joachimth/mk3-reference-loudspeaker/assets/datasheets/15W-4434G00.md

# ScanSpeak 15W/4434G00 — Datasheet Reference

**Source:** [Official ScanSpeak product page](https://www.scan-speak.dk/product/15w-4434g00/) + [official datasheet PDF (319KB)](./15W-4434G00.pdf) + ScanSpeak mounting drawing (embedded in PDF, extracted visually).

**Driver family:** Discovery series, 15 cm midwoofer, 4 Ω.
**Role in mk2:** Midrange driver.

---

## Mechanical dimensions (from official mounting drawing)

| Parameter | Value | Tolerance | Symbol / use in SCAD |
|---|---|---|---|
| Faceplate outer diameter | **149.3 mm** | ±0.5 | `mid_face_d` |
| Mounting BCD ("Pitch diam", 4-hole pattern) | **136.5 mm** | — | `mid_bcd` |
| Mounting hole diameter | **5.3 mm** | ±0.1 (×4 holes, 90° apart) | `mid_hole_d` |
| Number of mounting holes | **4** | — | `mid_holes` |
| Total depth (incl. front flange) | **61.9 mm** | — | `mid_depth` |
| Front flange thickness | **4.8 mm** | — | `mid_flange_t` (flush-mount rebate depth) |
| Basket / magnet system OD behind flange | **114 mm** (+2/0), Ø90 inner | — | `mid_basket_d` |
| Effective diaphragm diameter | 101 mm | — | (T-S only, not a mounting dim) |
| Cabinet displacement volume | **0.23 L** | — | `mid_displ_L` (datasheet "Mechanical Data") |
| Baffle cutout diameter | **not specified on drawing** — ~Ø123 estimate | — | `mid_cut_d` (must clear the Ø114 basket AND leave screw land inside the Ø136.5 BCD; caliper-verify) |

> **Source-of-truth:** values re-extracted July 2026 directly from the dimension
> drawing in `15W-4434G00.pdf`. An earlier version of this table (104.0 / 95.0 /
> 45.1 / Ø72 "rear cutout") did **not** match the official drawing — the Ø72
> figure led to a wrong `mid_cut_d` in `cabinet.scad` (a Ø72 hole is smaller than
> the Ø114 basket, so the driver could never be mounted). Ø149.3 faceplate,
> Ø136.5 pitch circle and 61.9 mm depth are printed on the drawing.

---

## Thiele-Small parameters (from official ScanSpeak product page)

| Parameter | Value | Unit | Use |
|---|---|---|---|
| Size | 15 | cm | — |
| Fs (resonance) | 43 | Hz | crossover HPF design |
| Re (DC resistance) | 3.0 | Ω | amplifier match, voice coil |
| Qt (total Q) | 0.21 | — | sealed/ported box sim |
| Sensitivity (2.83V / 1m) | 89.5 | dB | level matching vs tweeter/woofer |
| VAS (equivalent volume) | 12.8 | L | sealed box sizing |
| Sd (effective cone area) | 80 | cm² | displacement, SPL calcs |
| Bl (force factor) | 5.9 | T·m | motor strength |

---

## Open items / TODO

- [ ] **STEP / 3D model file** — ScanSpeak does not publish a STEP for this Discovery-series model. Need to:
  - either model manually from the mounting drawing (faceplate 149.3, BCD 136.5, 4×∅5.3 holes, total depth 61.9), OR
  - caliper-verify against a physical unit once received.

- [ ] **Baffle cutout diameter (`mid_cut_d`)** — set to **Ø123 (estimate)** in `cabinet.scad` (July 2026; the earlier Ø72 value came from the wrong table above and was physically impossible — smaller than the Ø114 basket). `cabinet.scad` echoes the remaining screw land and basket clearance automatically. **Next:** caliper-verify against a physical unit once received.

- [x] **Cabinet.scad integration** — `mid_face_d`, `mid_bcd`, `mid_hole_d`, `mid_depth`, `mid_flange_t`, `mid_basket_d`, `mid_cut_d`, `mid_displ_L` and T-S values (`mid_Fs`, `mid_Qts`, `mid_Vas_L`) are now parameters in `cad/cabinet.scad`, sourced from this file (cut hole, flush-mount rebate, pilot holes on the BCD, chamber volume + Qtc/Fc estimate).

- [ ] **Datasheet README source table** — add 15W/4434G00 row alongside H2606 with file path, Kilde, and "Open" status for STEP + cutout.

---

## Source files in this repo

- PDF: `assets/datasheets/15W-4434G00.pdf` (319 KB, official ScanSpeak)
- Frequency response CSV: `assets/datasheets/15W-4434G00_freq_response.csv` (on-axis + 2 off-axis, 100-10000 Hz, extracted from raster image)
- Impedance CSV: `assets/datasheets/15W-4434G00_impedance.csv` (impedance, 100-10000 Hz, extracted from raster image)
- Parameters CSV: `assets/datasheets/15W-4434G00_params.csv` (all T-S + mechanical parameters)
- Verification plot: `assets/datasheets/15W-4434G00_extraction_verify.png`
- Markdown reference: `assets/datasheets/15W-4434G00.md` (this file)
- SCAD integration: pending (see TODO above)

---

## Frequency response (extracted from datasheet)

On-axis + off-axis SPL, measured at 2.83V/1m. Data extracted from embedded raster image in PDF.

| Frequency | On-axis | Off-axis 1 | Off-axis 2 |
|---|---|---|---|
| 100 Hz | ~84 dB | — | — |
| 200 Hz | ~89 dB | ~89 dB | ~88 dB |
| 500 Hz | ~90 dB | ~90 dB | ~89 dB |
| 1 kHz | ~90 dB | ~89 dB | ~87 dB |
| 2 kHz | ~91 dB | ~88 dB | ~84 dB |
| 5 kHz | ~93 dB (peak) | ~82 dB | ~73 dB |
| 10 kHz | ~87 dB | ~65 dB | ~55 dB |

Full curves: `15W-4434G00_freq_response.csv` (1/12 octave resolution, on-axis + 2 off-axis curves)

## Impedance (extracted from datasheet)

| Frequency | Impedance |
|---|---|
| 100 Hz | 5.5 Ω |
| 300 Hz | 3.7 Ω (minimum) |
| 1 kHz | 5.5 Ω |
| 5 kHz | 9.5 Ω |
| 10 kHz | 13.7 Ω |

Full curve: `15W-4434G00_impedance.csv` (1/12 octave resolution, 100-10000 Hz)

> **Note:** No phase curve in ScanSpeak Discovery series datasheet. Impedance axis is log2 scale (1-64 Ω).
