joachimth/mk3-reference-loudspeaker/assets/datasheets/GRS-12SW-4HE.md

# GRS 12SW-4HE — 12" High Excursion Subwoofer

## Overview

GRS 12SW-4HE is a 12-inch high excursion subwoofer with a reinforced paper cone
and rubber surround. Selected as the woofer for the Mk3 Reference Loudspeaker
(v8), replacing the GRS 8SW-4HE-8 from v3-v7. Two units are used per enclosure
in a push-push configuration on the side panels.

## Datasheet

| File | Description |
|---|---|
| [GRS-12SW-4HE.pdf](GRS-12SW-4HE.pdf) | Official GRS spec sheet (646 KB) |

## Thiele/Small Parameters

| Parameter | Value | Notes |
|---|---|---|
| Nominal impedance | 4 Ω | |
| Re | 3.9 Ω | |
| Fs | 22 Hz | |
| Qms | 4.08 | |
| Qes | 0.48 | |
| Qts | 0.43 | |
| Vas | 80.4 L | |
| Sd | 504 cm² | |
| Xmax | 12.5 mm | Klippel verified (at 70% Bl) |
| Xmech | 21.9 mm | |
| Bl | 16.2 Tm | |
| Mms | 237 g | |
| Cms | 0.22 mm/N | |
| Le | 3.5 mH | |
| Voice coil | 50.8 mm (2") | 4-layer, aluminum former |
| Sensitivity | 84.5 dB @ 2.83V/1m | |
| Power handling | 250 W RMS (AES 426B) | |
| Frequency range | 20-500 Hz | |
| Net weight | 5.91 kg | |

## Mechanical Dimensions

| Dimension | Value |
|---|---|
| Overall diameter | Ø332 mm |
| Cutout diameter | Ø284 mm |
| Mounting holes | Ø5.5 (×8) at Ø319 BCD |
| Total depth | 136 mm |
| Voice coil diameter | 50.8 mm |

## Sealed Alignment (2× push-push)

| Vb (L) | Qtc | Fc (Hz) | F3 (Hz) |
|---|---|---|---|
| 69 | 0.78 | 40.1 | 36.6 |
| 75 | 0.76 | 39.0 | 36.4 |
| 80 | 0.75 | 38.2 | 36.3 |
| 85 | 0.73 | 37.4 | 36.2 |

With Linkwitz Transform (Fc → 28 Hz, Qtc → 0.707):
- Raw Fc 39 Hz → LT target 28 Hz
- Boost at 20 Hz: ~6 dB
- Max SPL @ 30 Hz: 109.5 dB (half-space, 1m, excursion-limited)

## Displacement

- Single driver: Vd = 6.3 cm³ (Sd 504 × Xmax 12.5 mm)
- Push-push pair: Vd = 12.6 cm³
- 6.3× more displacement than the previous GRS 8SW-4HE-8 pair (2.0 cm³)
- +16 dB max SPL at 30 Hz vs previous design

## Push-push Installation

Two 12SW-4HE are mounted opposed on the left and right side panels (370 mm deep).
With 284 mm cutout on 370 mm panel: 43 mm margin per side. Basket depth ~136 mm
each; internal width between side panels is 276 mm (300 - 2×22), leaving ~4 mm
gap between opposed magnet back plates. A coupling block bonds across the gap
for rigid mechanical coupling (push-push vibration cancellation).
