joachimth/mk3-reference-loudspeaker/assets/drawings/cut_list.pdf

## Mk3 Cabinet — Panel Cut List

Material: 22 mm birch plywood | External: 300 × 420 × 1180 mm
Panel | Width (mm) Height/Depth (mm) | Qty | Thickness | Notes
Front baffle | 300 | 1180 | 1 | 22 | R19 front vertical edges, mid + WG cutouts
Back panel | 300 | 1180 | 1 | 22 | Square edges
Side panel L | 420 | 1180 | 1 | 22 | Woofer cutout Ø284, 8×Ø5.5 on Ø319 BCD
Side panel R | 420 | 1180 | 1 | 22 | Woofer cutout Ø284, 8×Ø5.5 on Ø319 BCD (opposed)
Top panel | 300 | 420 | 1 | 22 | Square edges
Bottom panel | 300 | 420 | 1 | 22 | Square edges
Divider plate | 300 | 420 | 1 | 22 | Tilted 19°, cut to fit cavity
Shelf brace 1 | 256 | 376 | 1 | 22 | Ring shelf, rim 45 mm, z=160
Shelf brace 2 | 256 | 376 | 1 | 22 | Ring shelf, rim 45 mm, z=330
Shelf brace 3 | 256 | 376 | 1 | 22 | Ring shelf, rim 45 mm, z=730
Total panels: 10 | Total panel area: 2.37 m² | Plywood volume: 0.05 L
NOTE: Divider plate and shelf braces are cut to fit the internal cavity (256 × 376 mm). Measure
actual internal dims before cutting. All dimensions from cabinet.scad (single source of truth). Verify driver cutouts against datasheet
