joachimth/mk3-reference-loudspeaker/assets/renders/driver_woofer_template.png

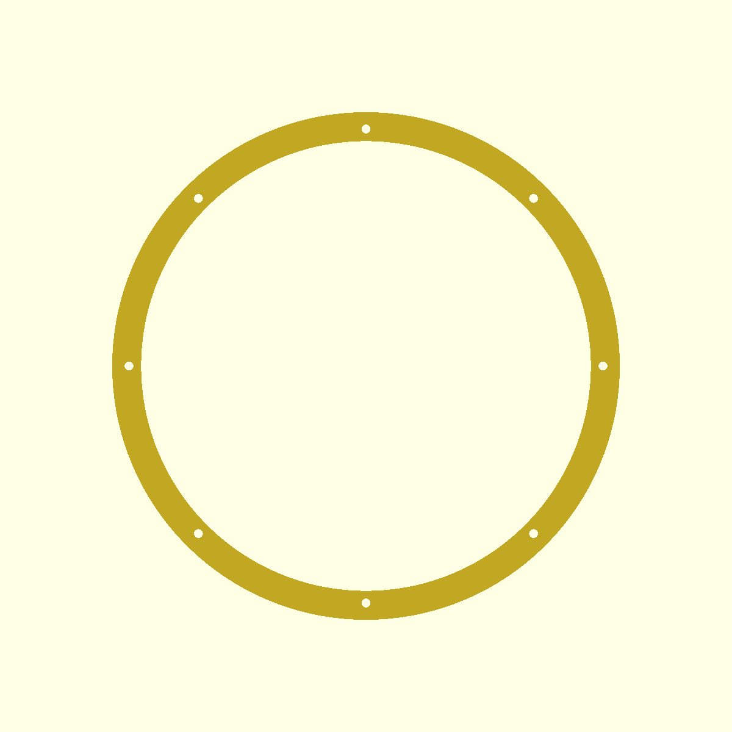
assets/renders/driver_woofer_template.png
