joachimth/mk3-reference-loudspeaker/simulations/plots/crossover_175_vs_200_decision.png

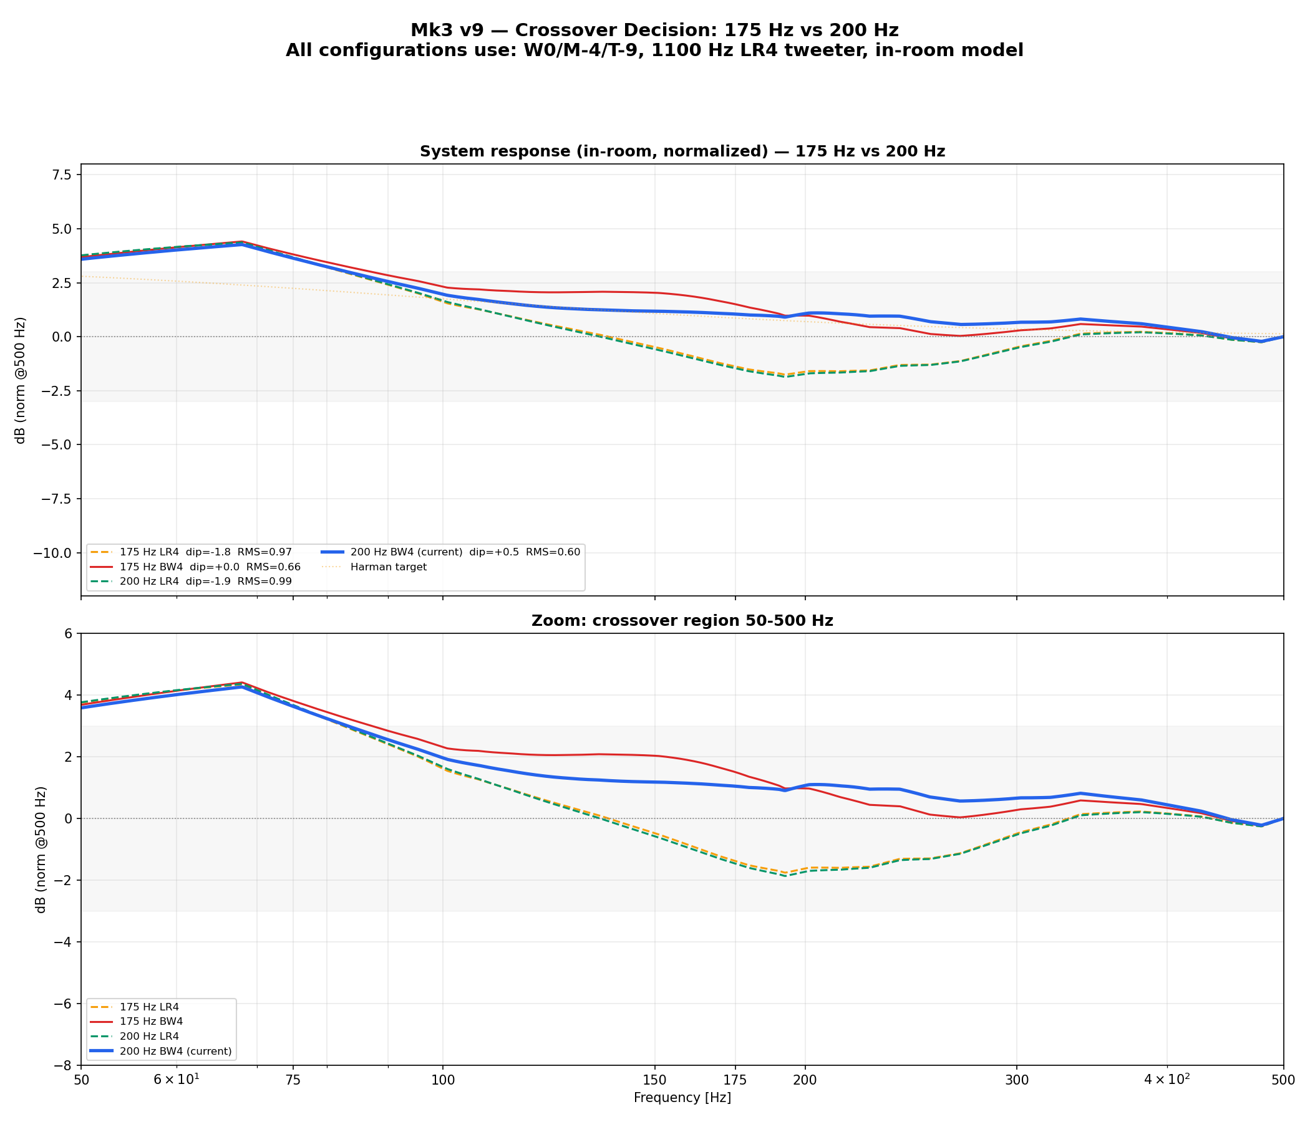
simulations/plots/crossover_175_vs_200_decision.png
