joachimth/mk3-reference-loudspeaker/simulations/plots/crossover_200_vs_175_inroom.png

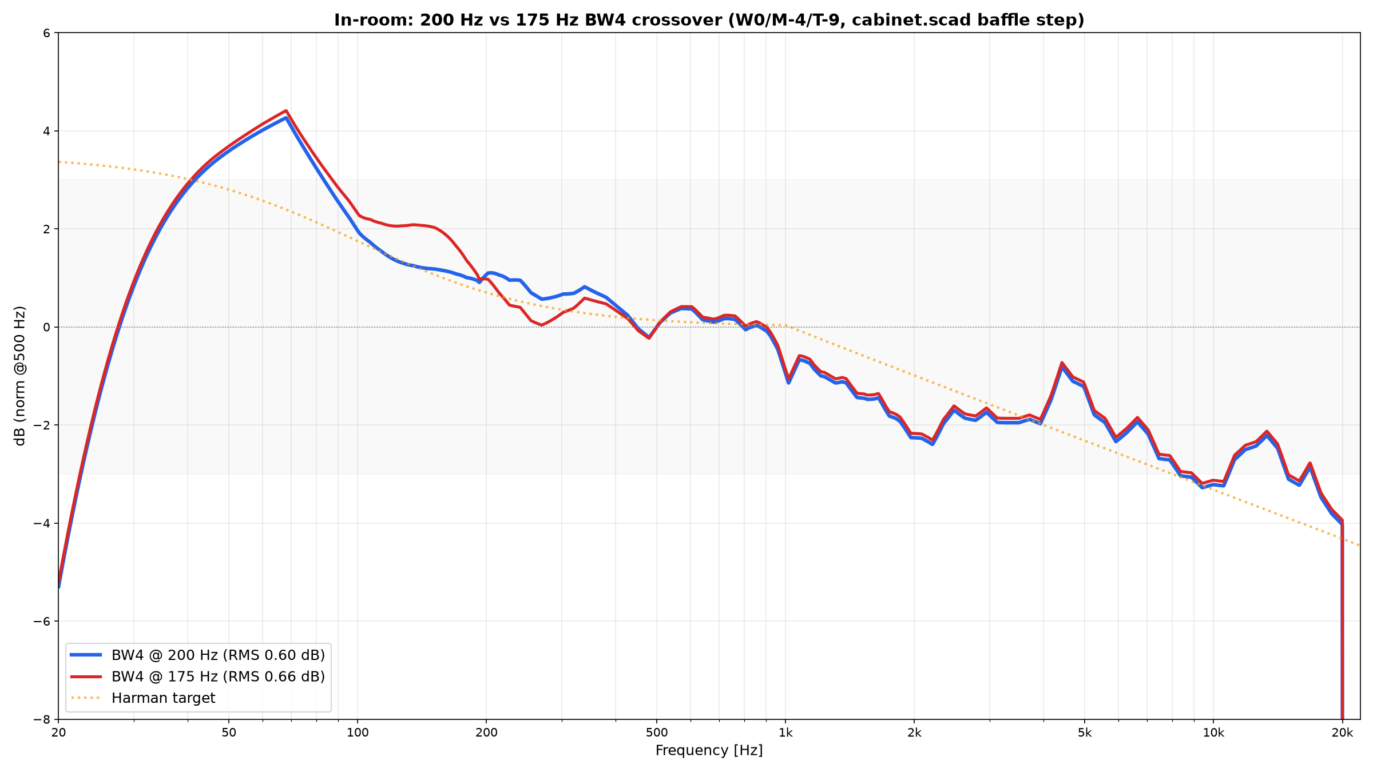
simulations/plots/crossover_200_vs_175_inroom.png
