joachimth/mk3-reference-loudspeaker/simulations/plots/crossover_200_vs_175_zoom.png

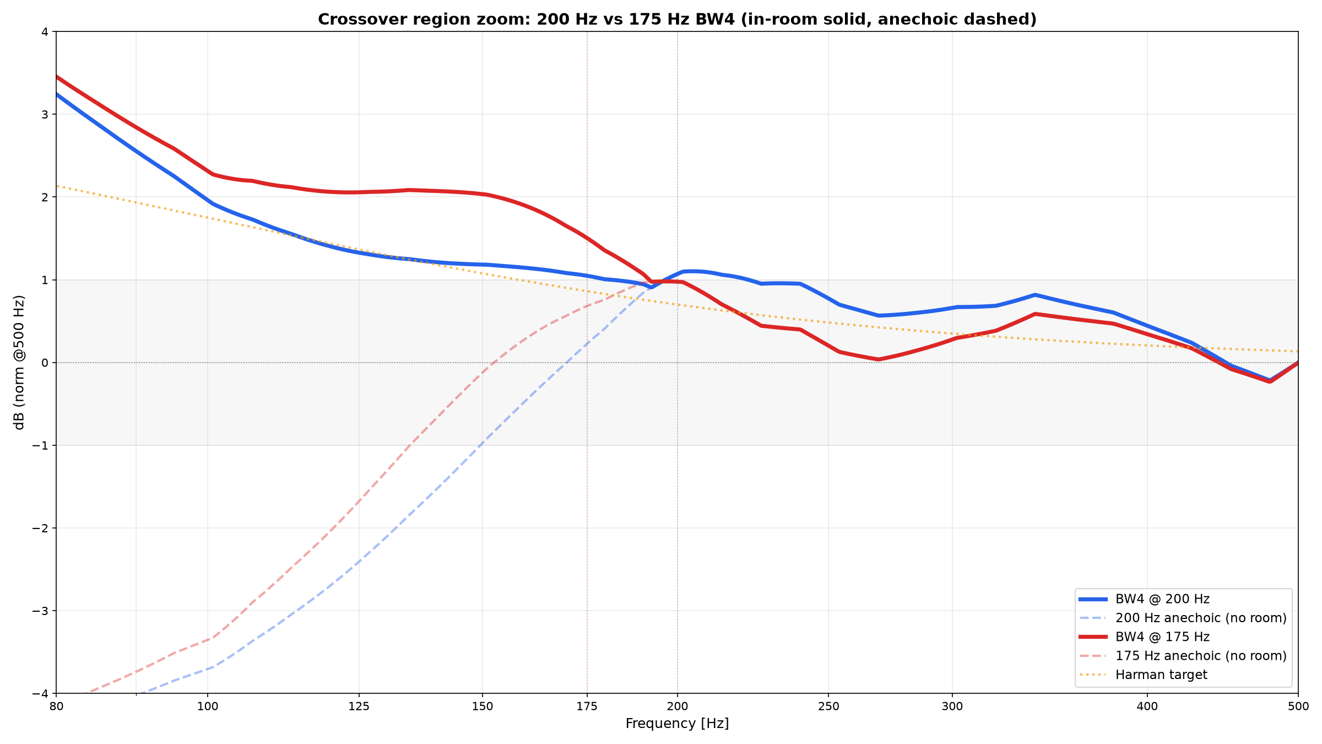
simulations/plots/crossover_200_vs_175_zoom.png
