joachimth/mk3-reference-loudspeaker/simulations/plots/inroom_all_gains_zero.png

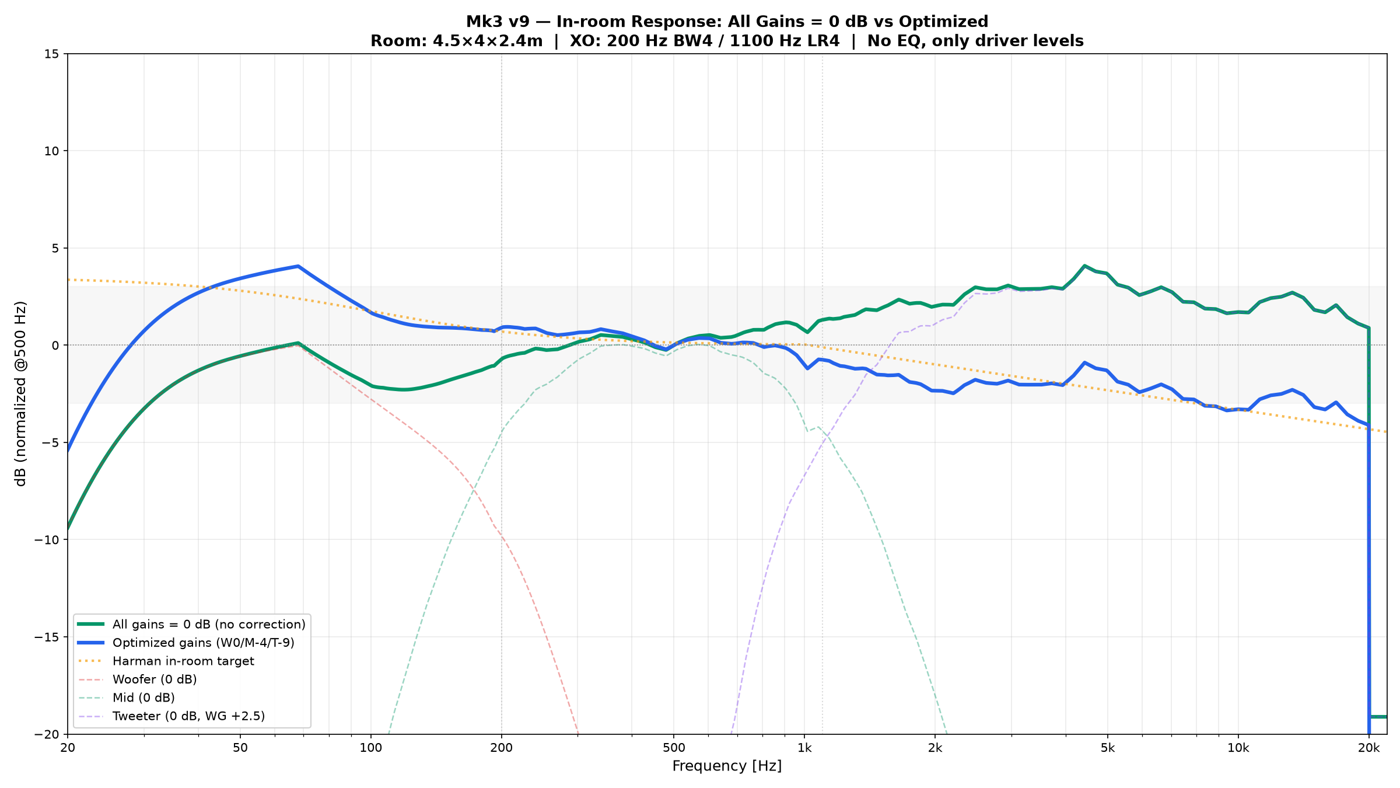
simulations/plots/inroom_all_gains_zero.png
