joachimth/mk3-reference-loudspeaker/simulations/plots/phase_analysis.png

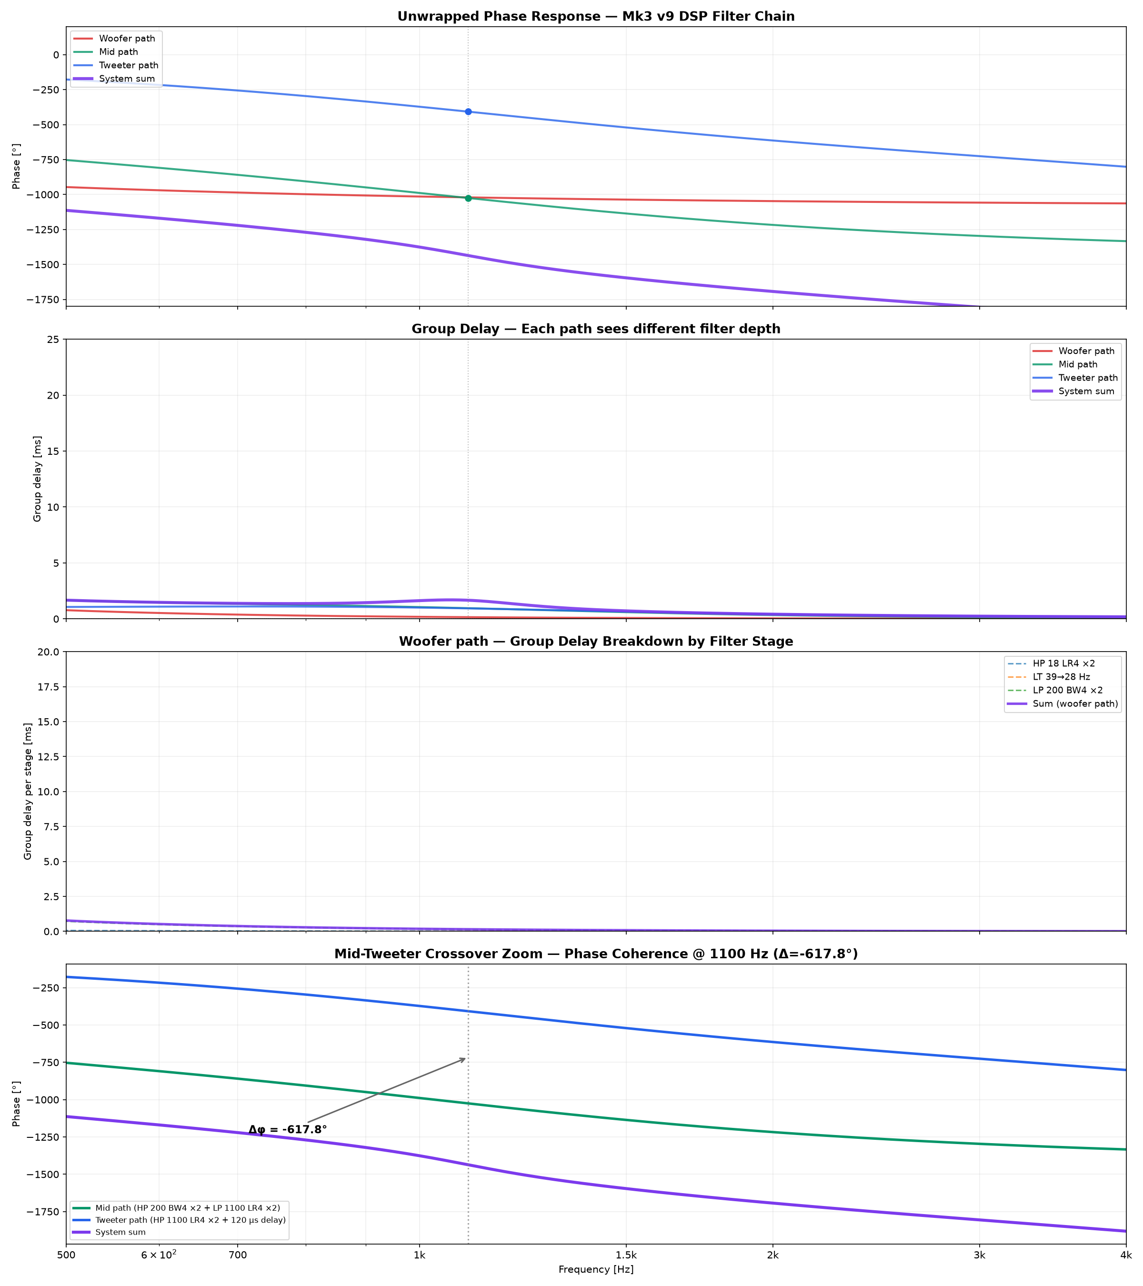
simulations/plots/phase_analysis.png
