joachimth/mk3-reference-loudspeaker/simulations/plots/radiation_pattern.png

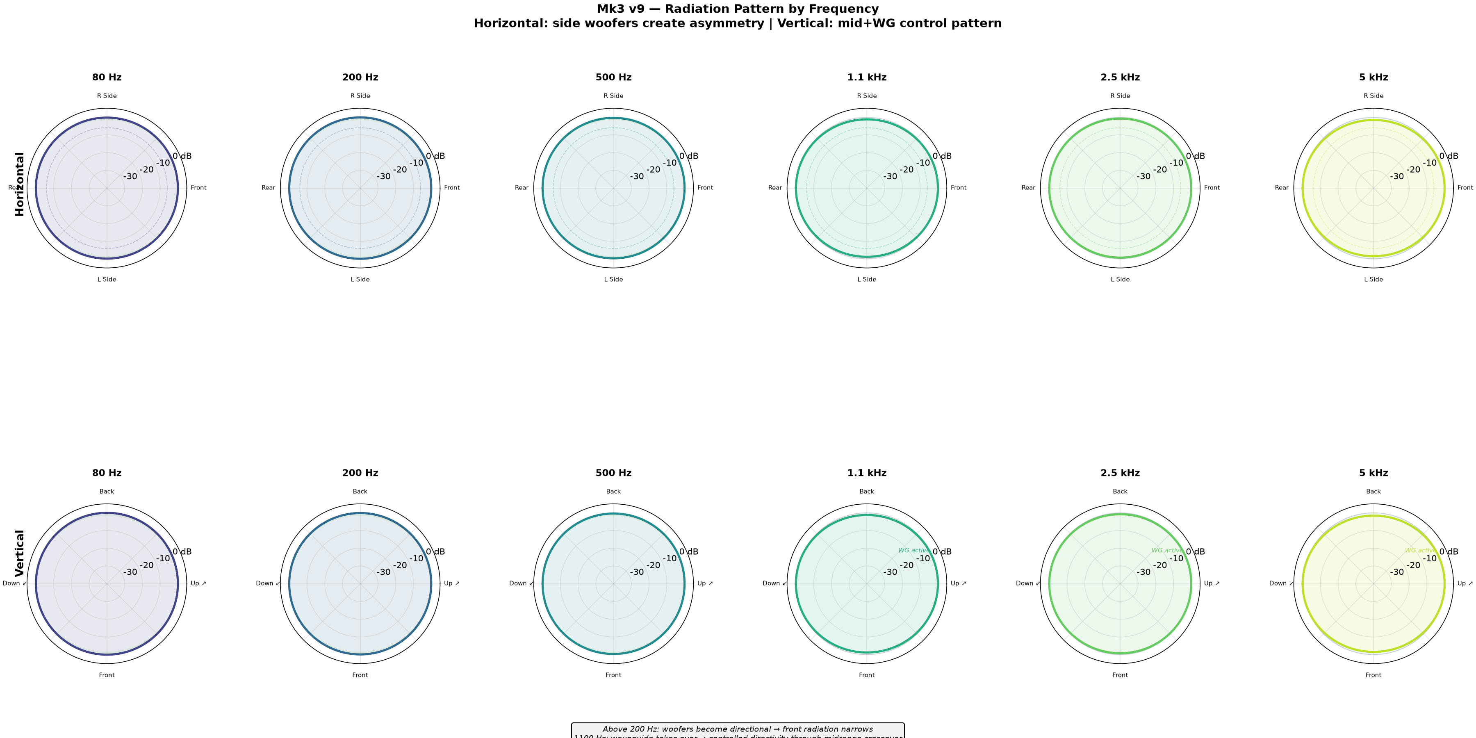
simulations/plots/radiation_pattern.png
